rprinz08/arty-s7-multinic/source/software/firmware/ci.c

#include <stdio.h>
#include <stdlib.h>
#include <string.h>

#include <irq.h>
#include <uart.h>
#include <console.h>
#include <generated/csr.h>
#include <generated/mem.h>

#include "config.h"
#include "reboot.h"
#include "system.h"
#include "uptime.h"
#include "network.h"
#include "ci.h"

const int RANDOM_RUNS = 500;
const int MALLOC_RUNS = 500;


static char *readstr(void)
{
    char c[2];
    static char s[64];
    static int ptr = 0;

    if(readchar_nonblock()) {
        c[0] = readchar();
        c[1] = 0;
        switch(c[0]) {
            case 0x7f:
            case 0x08:
                if(ptr > 0) {
                    ptr--;
                    putsnonl("\x08 \x08");
                }
                break;
            case 0x07:
                break;
            case '\r':
            case '\n':
                s[ptr] = 0x00;
                putsnonl("\n");
                ptr = 0;
                return s;
            default:
                if(ptr >= (sizeof(s) - 1))
                    break;
                putsnonl(c);
                s[ptr] = c[0];
                ptr++;
                break;
        }
    }

    return NULL;
}


static char *get_token(char **str)
{
    char *c, *d;

    c = (char *)strchr(*str, ' ');
    if(c == NULL) {
        d = *str;
        *str = *str+strlen(*str);
        return d;
    }
    *c = 0;
    d = *str;
    *str = c+1;
    return d;
}


static int get_number(const char *str) {
    return atoi(str);
}


static void help(void)
{
    puts("hello value      - Returns value xor'ed with 0xff in FPGA");
    puts("time             - show current clock ticks");
    puts("uptime           - show system uptime in seconds");
    printf("random [runs]    - show random number generator values, default [%d] runs\n",
            RANDOM_RUNS);
    printf("malloc [runs]    - test UMM malloc, default [%d] runs\n",
            MALLOC_RUNS);
    printf("ping             - ping host (%s) via network interface (%s)\n",
            ETH0_IP4_PING_ADDR, ETH0_NAME);
    puts("reboot           - reboot CPU");
    puts("help             - this command");
}

void ci_prompt(void)
{
    printf("HELLO >");
}

void ci_service(void)
{
    char *str;
    char *token;

    str = readstr();
    if(str == NULL)
        return;

    token = get_token(&str);
    if(strlen(token) < 1) {
        ci_prompt();
        return;
    }

    printf("\n");

    if(strcmp(token, "help") == 0) {
        puts("Available commands:");
        help();
        printf("\n");
    }
    else
    if(strcmp(token, "time") == 0) {
        printf("clk Hz        (%10lu)\n", cpu_clock_freq());
        printf("ticks         (%10lu)\n", ticks());
        printf("milliseconds  (%10lu)\n", ticks_milliseconds());
        printf("seconds       (%10lu)\n", ticks_seconds());
        printf("\n");
    }
    else
    if(strcmp(token, "uptime") == 0) {
        uptime();
        printf("\n");
    }
    else
    if(strcmp(token, "reboot") == 0) {
        reboot();
    }
    else
    if(strcmp(token, "random") == 0) {
        char *runs_raw = get_token(&str);
        int runs = get_number(runs_raw);

        if(runs < 0) {
            printf("Only positive numeric input\n\n");
            ci_prompt();
            return;
        }
        if(runs == 0)
            runs = RANDOM_RUNS;

        for(int i=0; i<runs; i++) {
            uint32_t rnd = random_random_read();
            printf("random #%d (%10lu) (0x%08x)\n",
                    i, rnd, rnd);
        }
        printf("\n");
    }
    else
    if(strcmp(token, "malloc") == 0) {
        // very simple malloc test

        const char *PAT = "abcdefghijklmnopqrstuvwxyz-ABCDEFGHIJKLMNOPQRSTUVWXYZ-0123456789-";
        const int LEN = strlen(PAT) + 12;

        char *runs_raw = get_token(&str);
        int runs = get_number(runs_raw);

        if(runs < 0) {
            printf("Only numeric input between 0 and %d!\n", MALLOC_RUNS);
            ci_prompt();
            return;
        }
        if(runs == 0)
            runs = MALLOC_RUNS;

        printf("malloc test %d bytes, %d runs\n",
                (LEN * runs), runs);

        // dont do this, this will break things!
        //char *m[runs];
        char **m = umm_malloc(runs * sizeof(char *));
        int i = 0;

        for(i=0; i<runs; i++) {
            printf("malloc %10d\r", i);
            m[i] = (char *)umm_malloc(LEN);
            if(m[i] == NULL) {
                printf("\nMalloc failed at run %d\n", i);
                break;
            }
            snprintf(m[i], LEN, "%s-%010d", PAT, i);
        }
        printf("\n");

        char buf[LEN];

        for(int j=0; j<runs; j++) {
            if(j == i)
                break;

            printf("free   %10d\r", j);
            snprintf(buf, LEN, "%s-%010d", PAT, j);
            if(strncmp(buf, m[j], LEN) != 0) {
                printf("\nMatch error at run %d, was (%s) should be (%s)\n",
                        j, m[j], buf);
            }
            umm_free(m[j]);
        }

        printf("\ndone\n");
    }
    else
	if(strcmp(token, "ping") == 0) {
		ping();
		printf("\n");
	}
	else
    // The 'hello' test command sends 8bit value to the input CSR of the
    // FPGA co-designed sample XOR module. Then reads back the value
    // XORed (in FPGA) with 0xff and displays the result
    if(strcmp(token, "hello") == 0) {
        char *val_raw = get_token(&str);
        int val = get_number(val_raw);
        if(val < 0 || val > 255) {
            printf("Only numeric input between 0 and 255!\n");
        }
        else {
            hello_input_write(val);
            uint8_t result = hello_output_read();
            printf("Write (%02x), Read (%02x)\n", val, result);
        }
        printf("\n");
    }
    else
        printf("Invalid command (%s)\n\n", token);

    ci_prompt();
}
