rprinz08/arty-s7-multinic/source/software/firmware/system.c

#include <stdio.h>
#include <generated/csr.h>
#include "system.h"


// configures UMM memory allocator
void *UMM_MALLOC_CFG_HEAP_ADDR = (void *)0x4ff00000;
uint32_t UMM_MALLOC_CFG_HEAP_SIZE = 1024 * 1024;


// defines ticker functions used by picotcp
uint32_t cpu_clock_freq(void)
{
    return config_clock_frequency_read();
}

uint32_t ticks(void)
{
    return ticker_ticks_read();
}

uint32_t ticks_milliseconds(void)
{
    return ticker_ms_read();
}

uint32_t ticks_seconds(void)
{
    return ticks_milliseconds() / 1000;
}
